MaffooClock/RadarLightControl/firmware/src/main.h

#ifndef _RLS_MAIN_H_
#define _RLS_MAIN_H_

#include <Arduino.h>
#include <time.h>

#include "pins.h"
#include "mode.h"
#include "oled.h"
#include "button.h"
#include "sensor.h"
#include "relay.h"

#endif
